aaron-nanas/FPGA-SoC-Robot-Car/3D_Models_Print_Files/RobotArm_V3_STL_Files/Channel_Connector_Plate_545532.stl

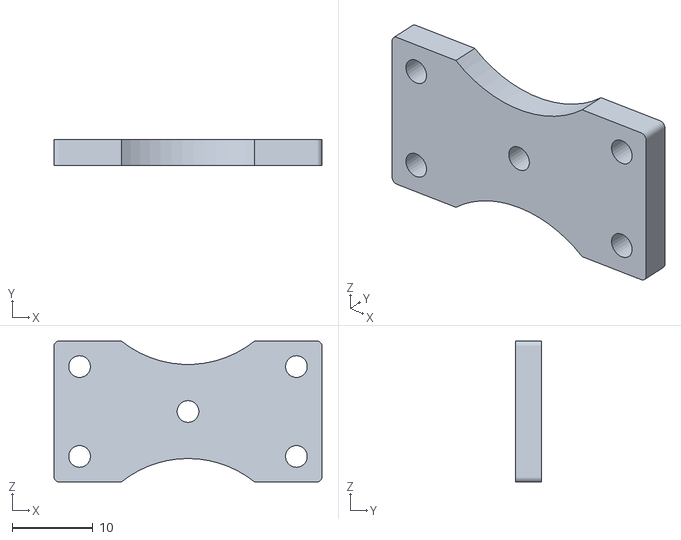
[picture p25: CAD file, 2021-11-11]
3D_Models_Print_Files/RobotArm_V3_STL_Files/Channel_Connector_Plate_545532.stl
33.3 x 3.17 x 17.5
