aaron-nanas/FPGA-SoC-Robot-Car/3D_Models_Print_Files/RobotArm_V3_STL_Files/1206-Series_Pattern_Adaptor_32-6.stl

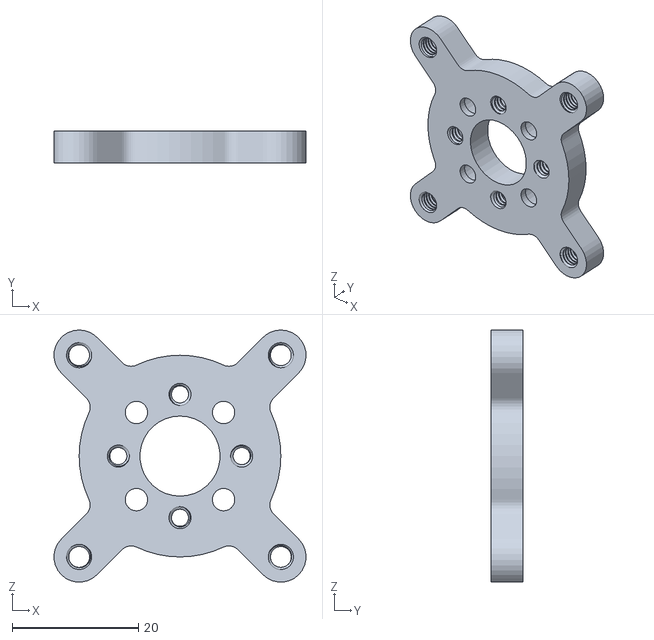
[picture p26: CAD file, 2021-11-11]
3D_Models_Print_Files/RobotArm_V3_STL_Files/1206-Series_Pattern_Adaptor_32-6.stl
40.0 x 5.00 x 40.0
