aaron-nanas/FPGA-SoC-Robot-Car/3D_Models_Print_Files/RobotArm_V3_STL_Files/tubeTest.stl

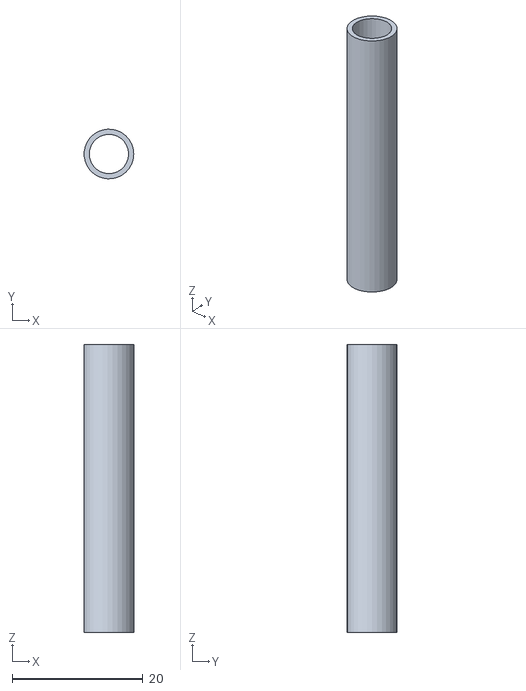
[picture p27: CAD file, 2021-11-11]
3D_Models_Print_Files/RobotArm_V3_STL_Files/tubeTest.stl
7.58 x 7.59 x 44.0
