aaron-nanas/FPGA-SoC-Robot-Car/3D_Models_Print_Files/RobotArm_V3_STL_Files/4mm-26mm_Tube.stl

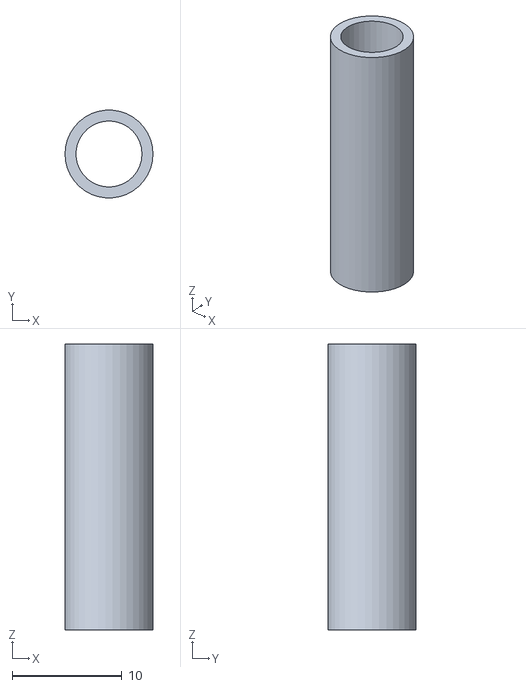
[picture p28: CAD file, 2021-11-11]
3D_Models_Print_Files/RobotArm_V3_STL_Files/4mm-26mm_Tube.stl
8.00 x 7.97 x 26.0
