aaron-nanas/FPGA-SoC-Robot-Car/3D_Models_Print_Files/RobotArm_V3_STL_Files/SideTapped_PatternMount_545360.stl

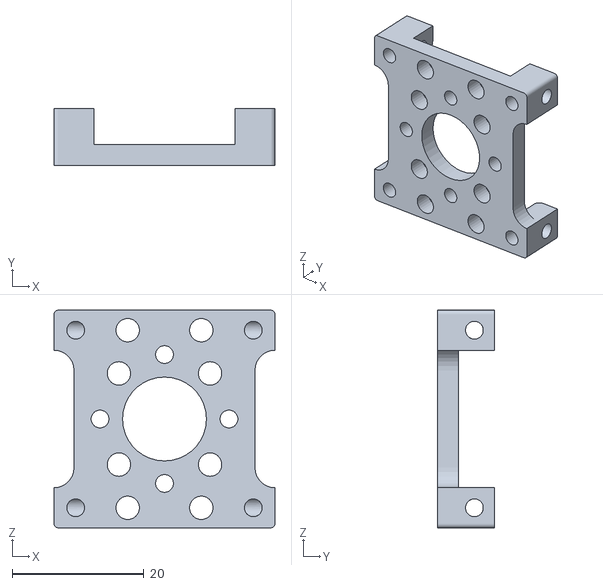
[picture p29: CAD file, 2021-11-11]
3D_Models_Print_Files/RobotArm_V3_STL_Files/SideTapped_PatternMount_545360.stl
33.5 x 8.63 x 33.0
