aaron-nanas/FPGA-SoC-Robot-Car/3D_Models_Print_Files/RobotArm_V3_STL_Files/4-50in_6in_Plate.stl

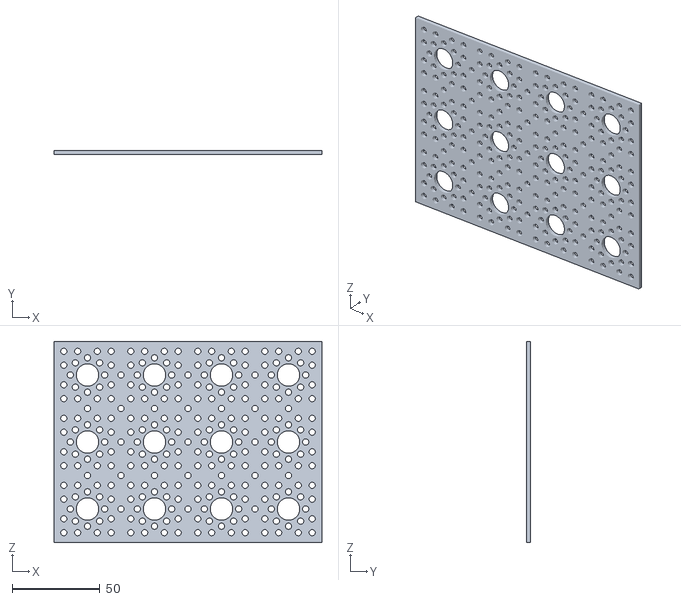
[picture p30: CAD file, 2021-11-11]
3D_Models_Print_Files/RobotArm_V3_STL_Files/4-50in_6in_Plate.stl
152.4 x 2.29 x 114.3
